OilSlick/coffee_tree_monitor/images/charger.jpg

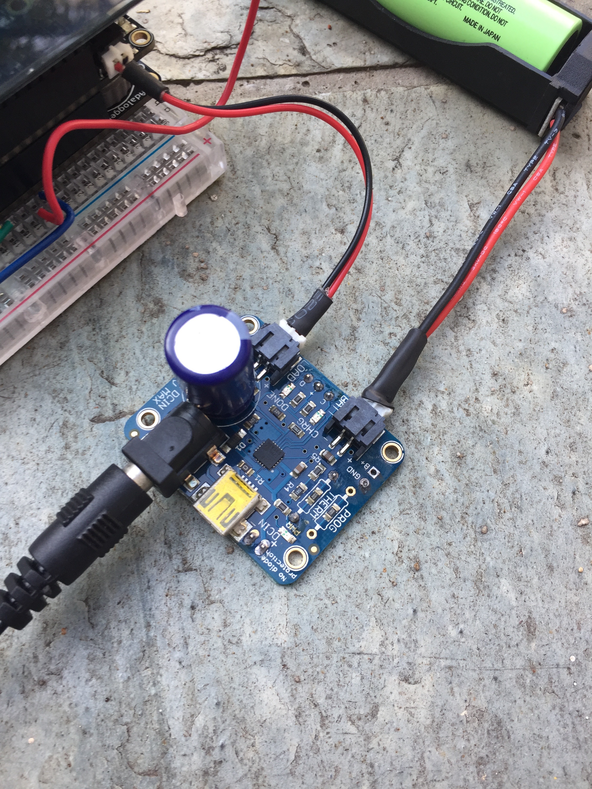
images/charger.jpg
