OilSlick/coffee_tree_monitor/images/IO_-_Feed__Lux.png

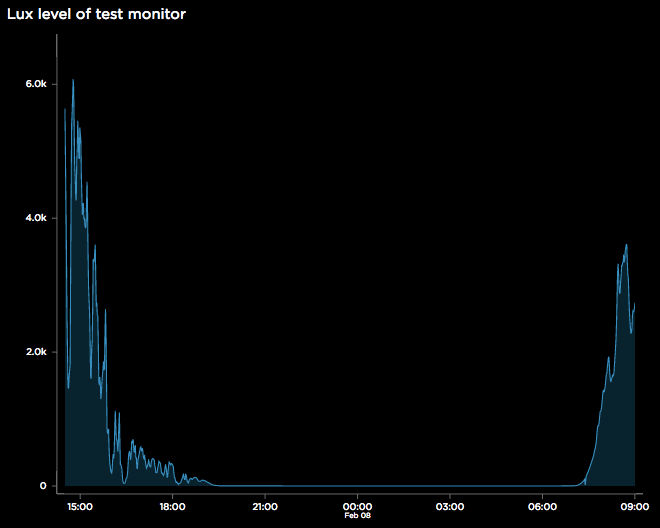
images/IO_-_Feed__Lux.png
