OilSlick/coffee_tree_monitor/images/lclv.jpg

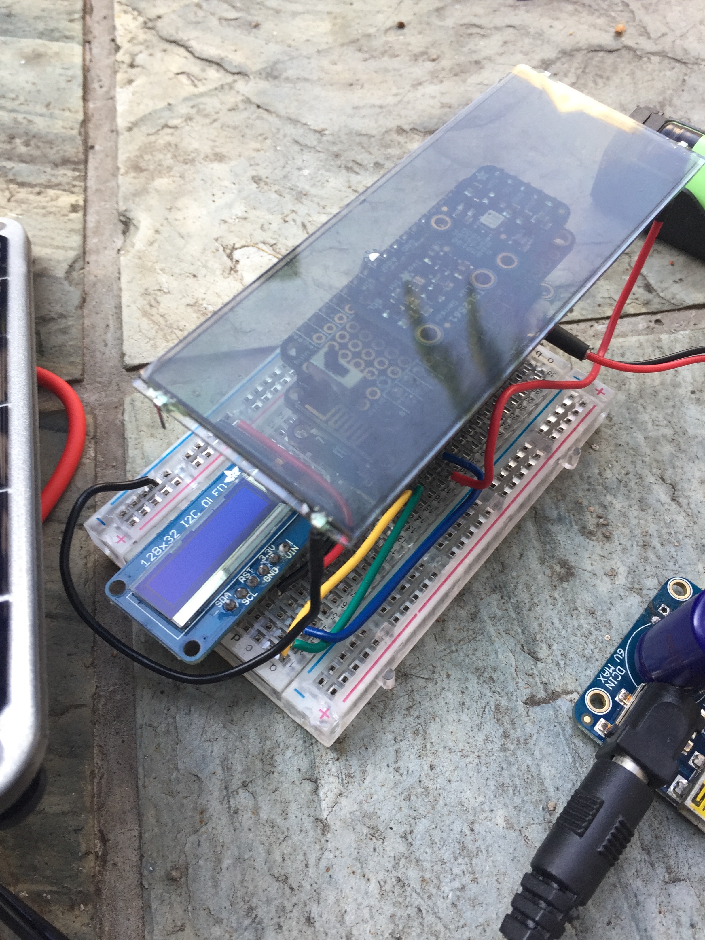
images/lclv.jpg
