OilSlick/coffee_tree_monitor/images/lux-max.png

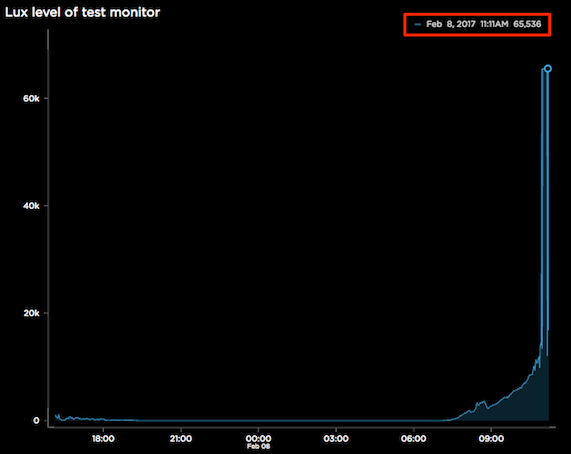
images/lux-max.png
