OilSlick/coffee_tree_monitor/images/oled.jpg

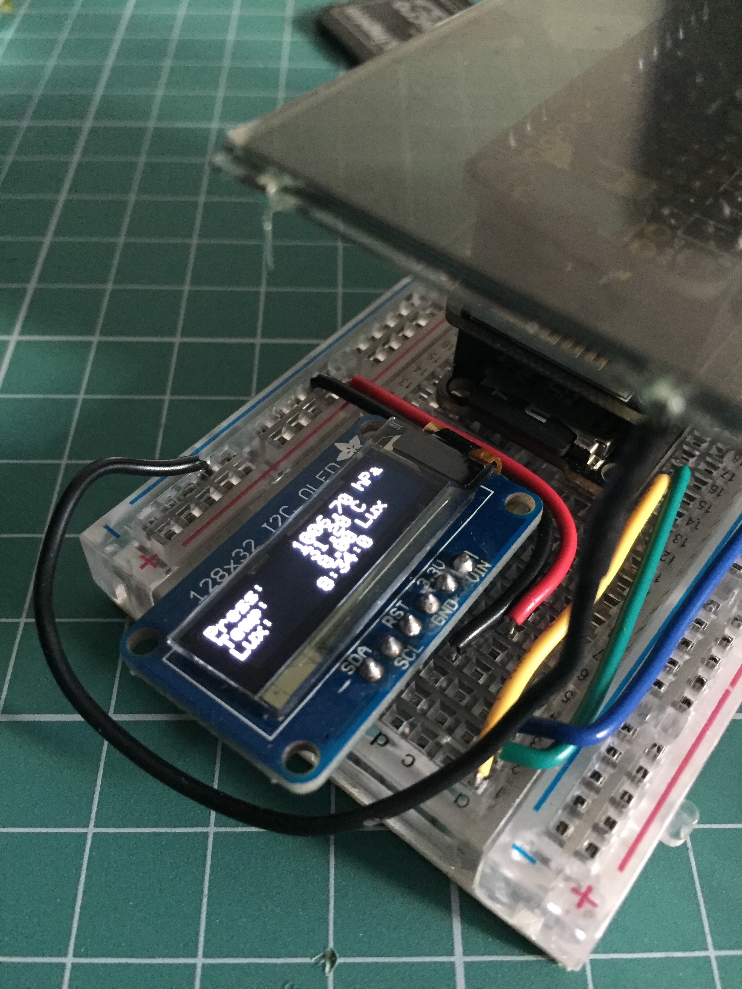
images/oled.jpg
